TobiasVanDyk/AtMega1284-PedalShield/images/Photo1.jpg

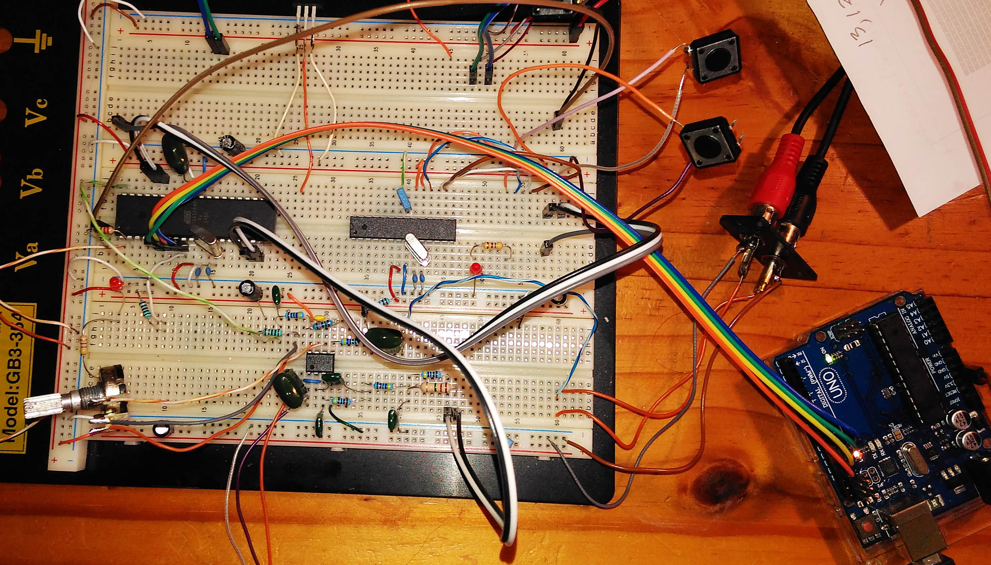
images/Photo1.jpg
